tanno1/beton-brut/images/3D_Back.png

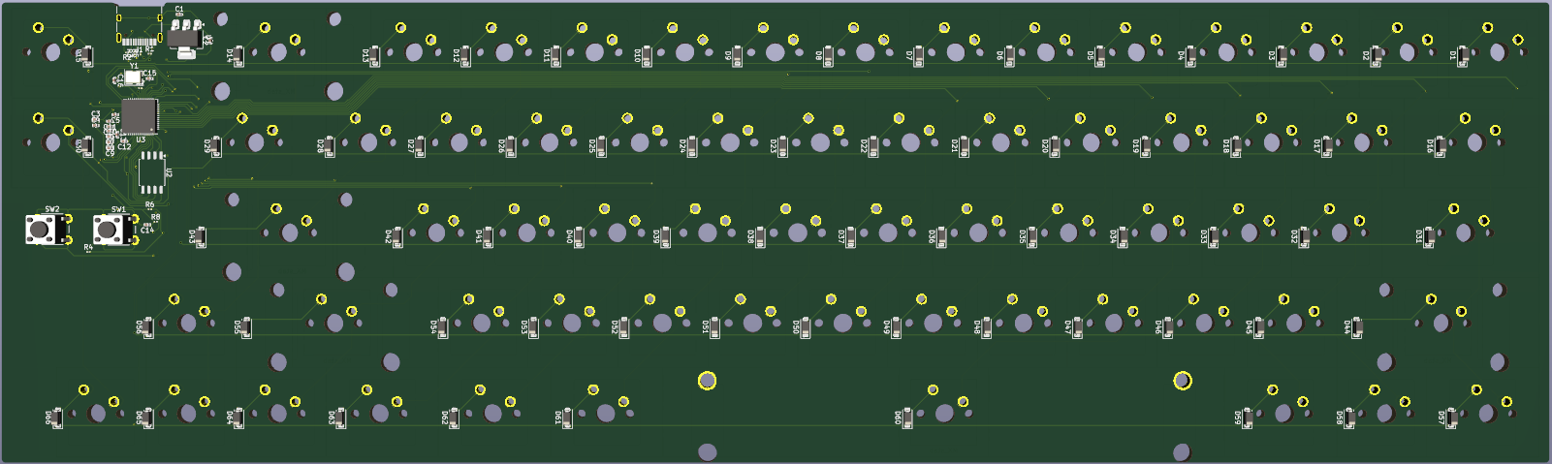
images/3D_Back.png
