tanno1/beton-brut/images/3D_Front.png

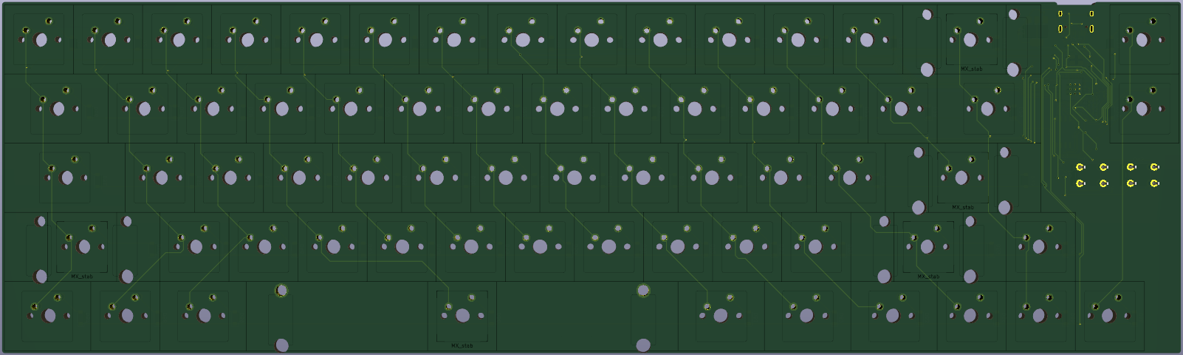
images/3D_Front.png
