tanno1/beton-brut/images/All_Cu_zoom.png

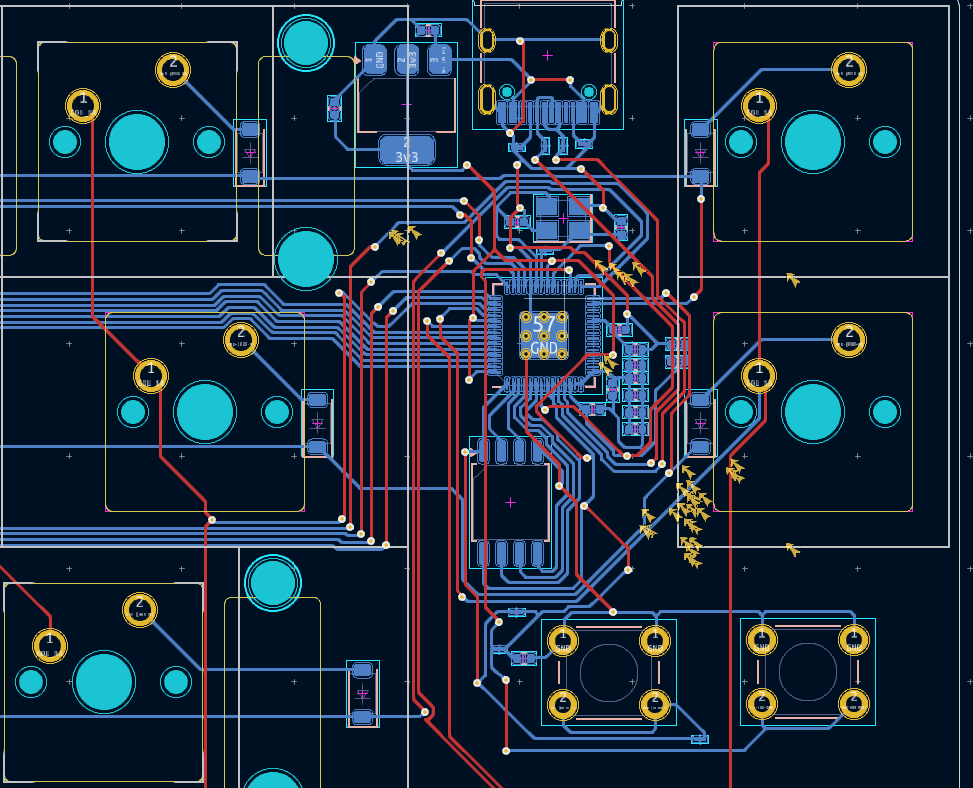
images/All_Cu_zoom.png
