tanno1/beton-brut/images/All_Layers.png

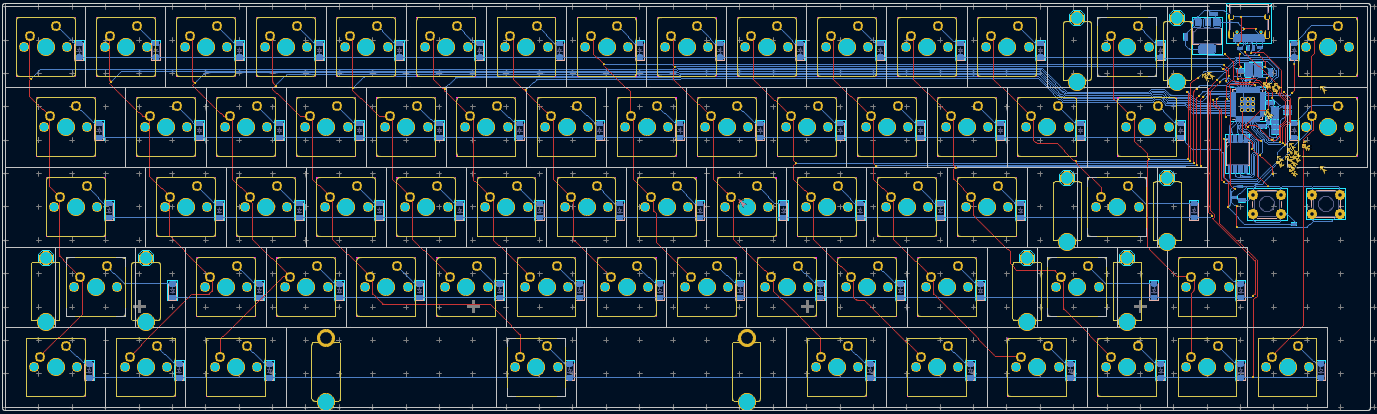
images/All_Layers.png
