tanno1/beton-brut/images/Back_Cu_zoom.png

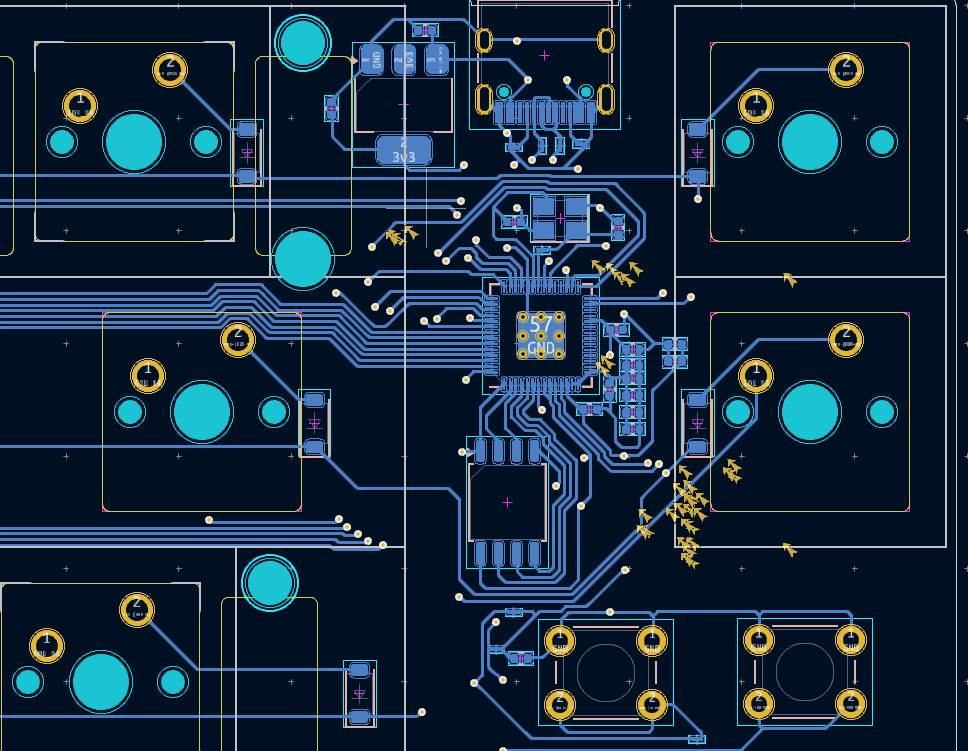
images/Back_Cu_zoom.png
