tanno1/beton-brut/images/closeright.jpg

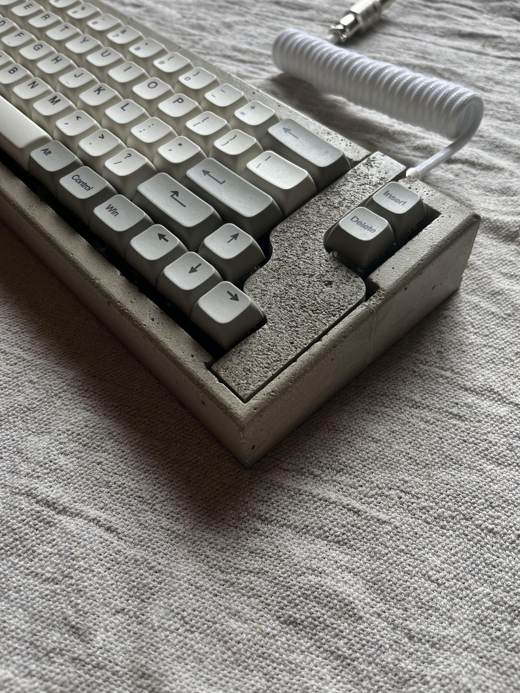
images/closeright.jpg
