tanno1/beton-brut/images/mold3.jpg

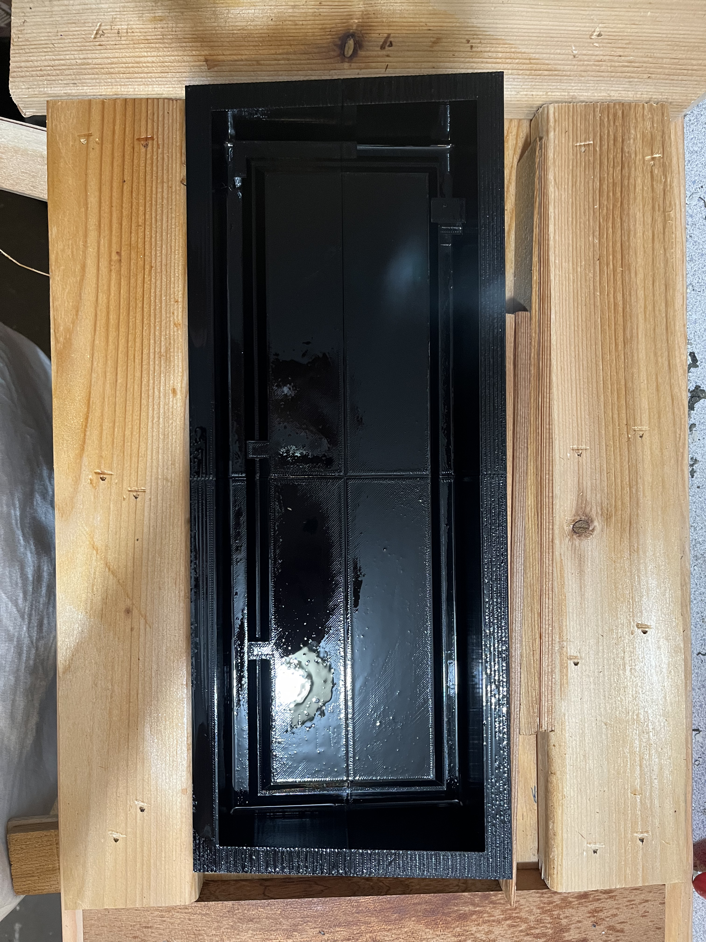
images/mold3.jpg
