tanno1/beton-brut/images/usbc.jpg

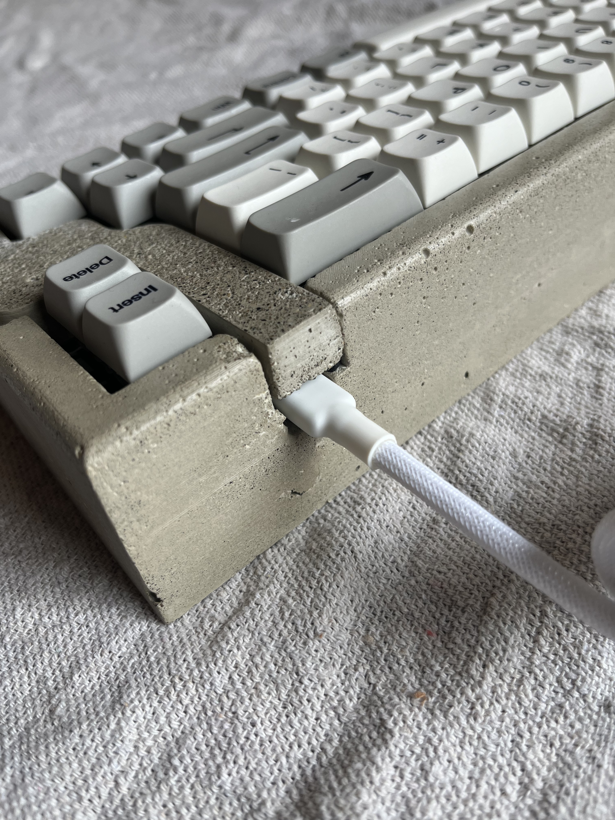
images/usbc.jpg
